innoveworkshop/MintyCharger/Firmware/src/config.h

/* 
 * config.h
 * Configures the microcontroller.
 * 
 * @author Nathan Campos <nathan@innoveworkshop.com>
 */

#ifndef CONFIG_H
#define	CONFIG_H

// Clock frequency.
#define _XTAL_FREQ 32000000

// CONFIG1
#pragma config FEXTOSC = OFF    // FEXTOSC External Oscillator mode Selection bits (Oscillator not enabled)
#pragma config RSTOSC = HFINT32 // Power-up default value for COSC bits (HFINTOSC with 2x PLL (32MHz))
#pragma config CLKOUTEN = OFF   // Clock Out Enable bit (CLKOUT function is disabled; I/O or oscillator function on OSC2)
#pragma config CSWEN = ON       // Clock Switch Enable bit (Writing to NOSC and NDIV is allowed)
#pragma config FCMEN = ON       // Fail-Safe Clock Monitor Enable (Fail-Safe Clock Monitor is enabled)

// CONFIG2
#pragma config MCLRE = OFF      // Master Clear Enable bit (MCLR/VPP pin function is digital input; MCLR internally disabled; Weak pull-up under control of port pin's WPU control bit.)
#pragma config PWRTE = OFF      // Power-up Timer Enable bit (PWRT disabled)
#pragma config WDTE = ON        // Watchdog Timer Enable bits (WDT enabled; SWDTEN is ignored)
#pragma config LPBOREN = OFF    // Low-power BOR enable bit (ULPBOR disabled)
#pragma config BOREN = OFF      // Brown-out Reset Enable bits (Brown-out Reset disabled)
#pragma config BORV = LOW       // Brown-out Reset Voltage selection bit (Brown-out voltage (Vbor) set to 2.45V)
#pragma config PPS1WAY = OFF    // PPSLOCK bit One-Way Set Enable bit (The PPSLOCK bit can be set and cleared repeatedly (subject to the unlock sequence))
#pragma config STVREN = ON      // Stack Overflow/Underflow Reset Enable bit (Stack Overflow or Underflow will cause a Reset)
#pragma config DEBUG = OFF      // Debugger enable bit (Background debugger disabled)

// CONFIG3
#pragma config WRT = OFF        // User NVM self-write protection bits (Write protection off)
#pragma config LVP = OFF        // Low Voltage Programming Enable bit (High Voltage on MCLR/VPP must be used for programming.)

// CONFIG4
#pragma config CP = OFF         // User NVM Program Memory Code Protection bit (User NVM code protection disabled)
#pragma config CPD = OFF        // Data NVM Memory Code Protection bit (Data NVM code protection disabled)

#endif	/* CONFIG_H */
