innoveworkshop/MintyCharger/Firmware/src/version.h

/**
 * version.h
 * Shows the user the current version of the firmware they are running.
 * 
 * @author Nathan Campos <nathan@innoveworkshop.com>
 */

#ifndef VERSION_H
#define	VERSION_H

extern inline void __attribute__((always_inline)) DisplayFirmwareInformation(void);

#endif	/* VERSION_H */
